dinoflorenzi/PC128-OLIVETTI-PRODEST-BIGROM/MULTI PAGE VERSION/IMG_20220428_181841.jpg

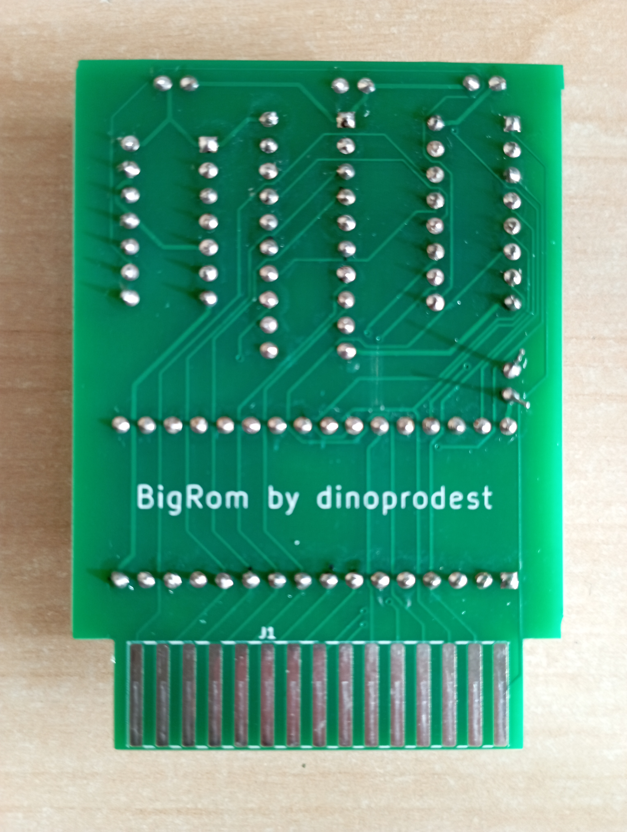
MULTI PAGE VERSION/IMG_20220428_181841.jpg
