dinoflorenzi/PC128-OLIVETTI-PRODEST-BIGROM/MULTI PAGE VERSION/IMG_20221108_195246.jpg

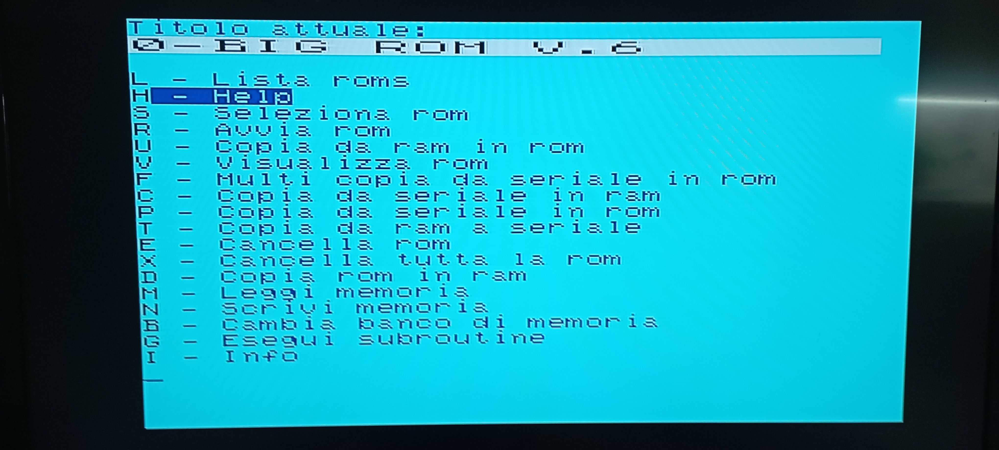
MULTI PAGE VERSION/IMG_20221108_195246.jpg
