dinoflorenzi/PC128-OLIVETTI-PRODEST-BIGROM/MULTI PAGE VERSION/IMG_20221108_195256.jpg

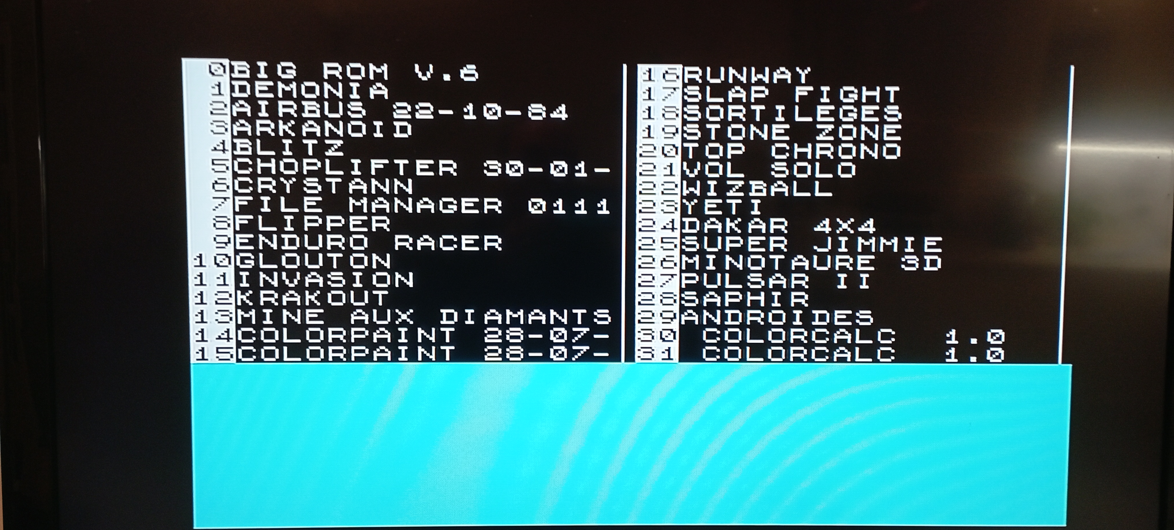
MULTI PAGE VERSION/IMG_20221108_195256.jpg
