dinoflorenzi/PC128-OLIVETTI-PRODEST-BIGROM/SERIAL-INTERFACE/IMG_20221204_191556.jpg

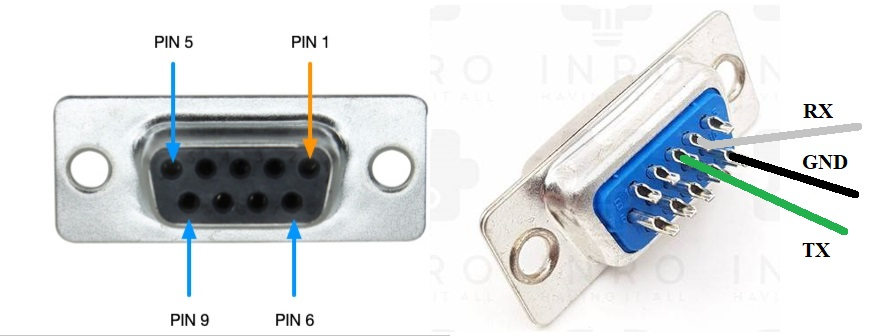
SERIAL-INTERFACE/IMG_20221204_191556.jpg
