dinoflorenzi/PC128-OLIVETTI-PRODEST-BIGROM/SINGLE PAGE VERSION/IMG_20220315_185737.jpg

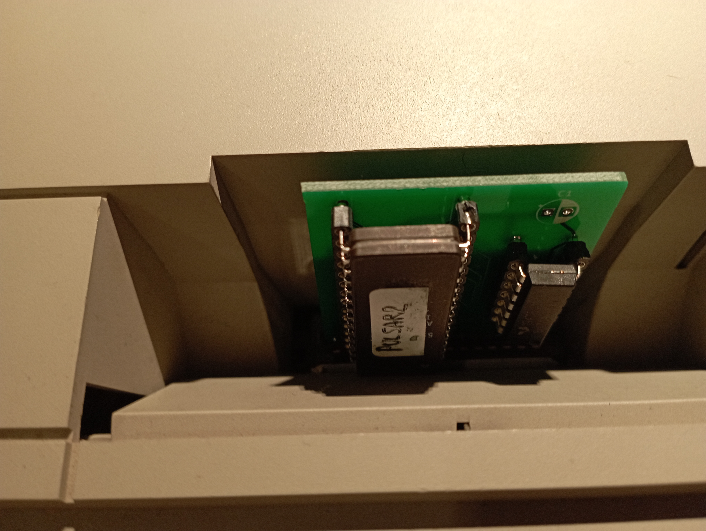
SINGLE PAGE VERSION/IMG_20220315_185737.jpg
