dinoflorenzi/PC128-OLIVETTI-PRODEST-BIGROM/SINGLE PAGE VERSION/IMG_20220315_185741.jpg

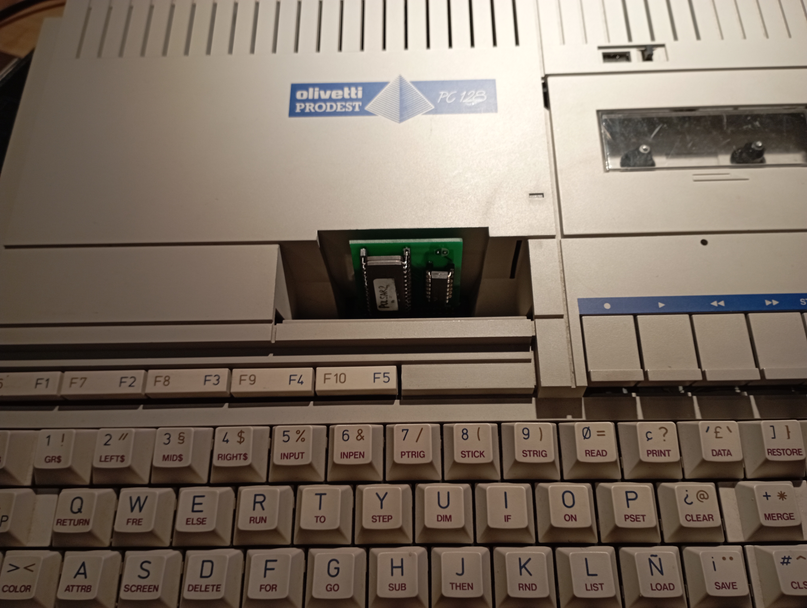
SINGLE PAGE VERSION/IMG_20220315_185741.jpg
